mikef5410/USB_PressureSensor/app/OSandPlatform.h

#ifndef _OSandPlatform_INCLUDED
#define _OSandPlatform_INCLUDED

#ifdef GLOBAL_OSandPlatform
#define OSandPlatformGLOBAL
#define OSandPlatformPRESET(A) = (A)
#else
#define OSandPlatformPRESET(A)
#ifdef __cplusplus
#define OSandPlatformGLOBAL extern "C"
#else
#define OSandPlatformGLOBAL extern
#endif	/*__cplusplus*/
#endif				/*GLOBAL_OSandPlatform */

#ifdef __cplusplus
extern "C" {
#endif


/// \addtogroup lowlevel
/// @{
#include <FreeRTOS.h>
#include <task.h>
#include <queue.h>
#include <semphr.h>
#include <timers.h>

//#pragma GCC diagnostic push
//#pragma GCC diagnostic ignored "-Wpointer-sign"
//#pragma GCC diagnostic pop

#include <stdlib.h>
#include <stdarg.h>
#include <stdio.h>
#include <ctype.h>
#include <string.h>
#include <math.h>
#include <stdint.h>
#include <strings.h>
#include <limits.h>
#include <malloc.h>
#include <machine/endian.h> // /opt/gcc-arm-none-eabi-5_4-2016q3/arm-none-eabi/include/machine

#include <libopencmsis/core_cm3.h>
#include <libopencm3/stm32/gpio.h>
#include <libopencm3/stm32/rcc.h>
#include <libopencm3/cm3/scb.h>
#include <libopencm3/cm3/systick.h>
#include <libopencm3/cm3/nvic.h>
#include <libopencm3/usb/usbd.h>
#include <libopencm3/stm32/flash.h>
#include <libopencm3/stm32/desig.h>
#include <libopencm3/stm32/spi.h>
#include <libopencm3/stm32/i2c.h>
  
#include <libopencm3/stm32/f3/nvic.h>
  
#include "version.h"
#include "endian.h"
#include "bsp.h"  
#include "hiresTimer.h"
#include "usbcmdio.h"
#include "instr_task.h"  
  
#define TESTEEPROM 1
#include "eeprom9366.h"
#include "ms8607.h"
#include "SSCDANN150PG2A3.h"

//#define CEXCEPTION_USE_CONFIG_FILE
//#include "CException.h"

#ifdef __cplusplus
extern "C" {
#endif

//Chip driver status return values
typedef int32_t ChipDriverStatus_t;

#define SUCCESS 0
#define FAILURE 1
#define DO_NOT_TX -1
#define SATURATED 101
#define TRUE 1
#define FALSE 0
  
#ifndef RELEASE
#define ASSERT(EXPR) assert(EXPR)
#else
#define ASSERT(EXPR)
#endif

#define likely(x)       __builtin_expect((x),1)
#define unlikely(x)     __builtin_expect((x),0)

#ifndef MIN
#define MIN(a,b) (a<=b)?(a):(b)
#endif

#ifndef MAX  
#define MAX(a,b) (a>=b)?(a):(b)
#endif
  
//Trigger a HARD FAULT by writing to a FLASH ROM location
#define TRIG_HARDFAULT *((volatile int*)(0x8000000))=0
    
//We'll define this later
    typedef void BaseSequentialStream;

// HACK HACK HACK
// TEMPORARY HACK TO MAKE PRINTF WORK WITHIN FREERTOS TASKS
    OSandPlatformGLOBAL char pbuf[1024];
    extern int myprintf(const char *format, ...);
    extern int mysprintf(char *out, const char *format, ...);
    extern int mysnprintf(char *buf, unsigned int count,
			  const char *format, ...);

#define ENABLE_DEBUG_TASK 1

#ifdef RELEASE
#define DPRINTF(...)
#define FDPRINTF(FILE,...)
#define dprintf(...)
#else
#define DPRINTF(...) myprintf(__VA_ARGS__)
#define FDPRINTF(FILE,...) myprintf(__VA_ARGS__)
#define dprintf(...) myprintf(__VA_ARGS__)
#endif


#define delayms(x) do { if (xTaskGetSchedulerState() == taskSCHEDULER_RUNNING) { \
    vTaskDelay((x)/portTICK_RATE_MS);                                   \
  } else { \
    MSleep(x); \
  }  } while(0)


  
typedef struct task_info {
  uint32_t ExceptionTaskID;
} task_info_t;
    
OSandPlatformGLOBAL uint32_t numRegisteredTasks;	//main.c


extern char __StackTop;
extern char __StackLimit;
extern char __heap_start;
extern char __heap_end;

#ifdef __cplusplus
}
#endif

#endif				//OSandPlatform_INCLUDED

/// @}
