mikef5410/USB_PressureSensor/app/eeprom9366.c

/*******************************************************************************
*           Copyright (C) 2015 Michael R. Ferrara, All rights reserved.
*
*                       Santa Rosa, CA 95404
*                       Tel:(707)536-1330
*
* Filename:     eeprom9366.c
*
* Description: EEPROM9366 "driver"
*
*******************************************************************************/
//#define TRACE_PRINT 1

#include "OSandPlatform.h"

#define GLOBAL_EEPROM9366
#include "eeprom9366.h"

// This device has 9 bits of address, led by a three bit cmd.
// Data is 8 bit bytes.


static uint32_t writeEnabled = 0;

static inline void assertCS()
{
  //taskENTER_CRITICAL();
  gpio_set(GPIOB,GPIO9);
  //delayms(1); //Tcss
  return;
}

static inline void deassertCS()
{
  delayms(1); //Tcsl
  gpio_clear(GPIOB,GPIO9);
  //taskEXIT_CRITICAL();
  return;
}

static inline uint8_t spiTransaction(uint8_t command, uint16_t address, uint8_t data)
{
  uint8_t rbyte = 0;

  uint8_t b1 = (command<<2) | ((address & 0x180)>>7);
  uint8_t b2 = (address & 0x7f)<<1 | ((data & 0x80)>>7); 
  uint8_t b3 = (data & 0x7f)<<1;
  
  //printf("OUT: 0x%02x, 0x%04x, 0x%02x\n",command, address, data);
  //printf("Trans: 0x%02x 0x%02x 0x%02x\n",b1,b2,data);

  //Wait for Tx empty
  while (!(SPI_SR(SPI2) & SPI_SR_TXE));
  rbyte = SPI_DR(SPI2); // Clear the rx buffer
  rbyte = SPI_DR(SPI2); // Clear the rx buffer
  rbyte = SPI_DR(SPI2); // Clear the rx buffer
  rbyte = SPI_DR(SPI2); // Clear the rx buffer
  
  assertCS();
  // Byte 1 ... 3 bits of command + 9th bit of address
  spi_send8(SPI2,b1);
  (void)spi_read8(SPI2);

  // Byte 2 ... 8 bits of address,
  spi_send8(SPI2,b2);
  (void)spi_read8(SPI2);
 
  // Byte 3
  spi_send8(SPI2,b3);
  rbyte=spi_read8(SPI2);
  deassertCS();

  return(rbyte);
}

static inline void spiCMD(uint8_t command, uint16_t address)
{

  uint8_t b1 = (command<<1) | ((address & 0x100)>>8);
  uint8_t b2 = address & 0xff;
  uint8_t r;
  //printf("OUT: 0x%02x, 0x%02x\n",command, address);
  //printf("Trans: 0x%02x 0x%02x\n",b1,b2);

  //Wait for Tx empty
  while (!(SPI_SR(SPI2) & SPI_SR_TXE));
  r = SPI_DR(SPI2); // Clear the rx buffer
  r = SPI_DR(SPI2); // Clear the rx buffer
  r = SPI_DR(SPI2); // Clear the rx buffer
  r = SPI_DR(SPI2); // Clear the rx buffer
  (void)r;
  
  assertCS();
  
  // Byte 1 ... 3 bits of command + 1 bit of address
  spi_send8(SPI2,b1);
  (void)spi_read8(SPI2);
  
  // Byte 2 ... 8 bits of address
  spi_send8(SPI2,b2);
  (void)spi_read8(SPI2);
  
  deassertCS();
  return;
}

static inline void writeEnable()
{
  if (writeEnabled) return;
  spiCMD(0x4,0x180);
  writeEnabled=1;
  return;
}

EEPROM9366GLOBAL void eeprom9366_eraseAll()
{
  writeEnable();
  spiCMD(0x4, 0x100);
  delayms(10);
}

EEPROM9366GLOBAL void eeprom9366_erase(uint16_t address)
{
  writeEnable();
  spiCMD(0x7,address);
  delayms(10);
  return;
}


EEPROM9366GLOBAL void eeprom9366_write(uint16_t address, uint8_t data)
{
  writeEnable();
  (void)spiTransaction(0x5,address,data);
  delayms(10);
  return;
}


EEPROM9366GLOBAL uint8_t eeprom9366_read(uint16_t address)
{
  uint8_t res = spiTransaction(0x6,address,0);
  return(res);
}

EEPROM9366GLOBAL void eeprom9366_init()
{

  //SPI2 pins for EEPROM (Alternate function 5)
  //PB9 is SPI2NSS, PB8 is SPI2SCK
  //PB14 is SPI2MISO, PB15 SPI2MOSI
  //PCLK is 72MHz, so we need to select a baud rate divider
  //such that SPI CLK is less than 2MHz (32 -> 1.5MHz)
  rcc_periph_clock_enable(RCC_SPI2);
  gpio_mode_setup(GPIOB, GPIO_MODE_OUTPUT, GPIO_PUPD_NONE, GPIO9); //Software Slave-Select
  gpio_clear(GPIOB,GPIO9);
  gpio_set_output_options(GPIOB, GPIO_OTYPE_PP, GPIO_OSPEED_100MHZ, GPIO9);
  
  gpio_mode_setup(GPIOB, GPIO_MODE_AF, GPIO_PUPD_NONE,
                  GPIO8 | GPIO14 | GPIO15);
  gpio_set_af(GPIOB, GPIO_AF5, GPIO8 | GPIO14 | GPIO15);
  //gpio_set_output_options(GPIOB, GPIO_OTYPE_PP, GPIO_OSPEED_100MHZ,
  //                               GPIO8 | GPIO15); //SCK and MOSI are driven
  

  spi_set_master_mode(SPI2);
  spi_set_baudrate_prescaler(SPI2, SPI_CR1_BR_FPCLK_DIV_64); // 72/64 = 1.125MHz
  spi_set_clock_polarity_0(SPI2);
  spi_set_clock_phase_0(SPI2);
  spi_set_full_duplex_mode(SPI2);
  spi_set_unidirectional_mode(SPI2); /* bidirectional but in 3-wire */
  spi_set_data_size(SPI2, SPI_CR2_DS_8BIT);
  spi_enable_software_slave_management(SPI2);
  spi_send_msb_first(SPI2);
  spi_set_nss_high(SPI2);
  //spi_enable_ss_output(SPI2);
  spi_fifo_reception_threshold_8bit(SPI2);
  SPI_I2SCFGR(SPI2) &= ~SPI_I2SCFGR_I2SMOD;
  spi_enable(SPI2);
  spi_disable_crc(SPI2);
  spi_set_next_tx_from_buffer(SPI2);
 
  return;
}

#ifdef TESTEEPROM
EEPROM9366GLOBAL void eeprom9366_test()
{

  uint8_t d;
  
  printf("SPI_CR1: 0x%04x\n",(uint16_t)SPI_CR1(SPI2));
  printf("SPI_CR2: 0x%04x\n",(uint16_t)SPI_CR2(SPI2));
  printf("SPI_SR: 0x%04x\n",(uint16_t)SPI_SR(SPI2));
 
  myprintf("EEProm Test\n");
  eeprom9366_eraseAll();
  myprintf("Erase complete\n");
  d = eeprom9366_read(0x10);
  myprintf("EEPROM read after erase: 0x%x\n",d);
  eeprom9366_write(0x10,0x41);
  d = eeprom9366_read(0x10);
  myprintf("EEPROM read after write (0x41): 0x%x\n",d);
  d = eeprom9366_read(0x11);
  myprintf("EEPROM read after write of next cell : 0x%x\n",d);

  eeprom9366_write(0x11,0x01);
  eeprom9366_write(0x12,0x2);
  eeprom9366_write(0x13,0x3);

  printf("Write/read block ... should be 0x41,1,2,3,0xff:\n");
  uint8_t a;
  for (a=0x10; a<=0x14; a++) {
    d= eeprom9366_read(a);
    printf(" 0x%02x",d);
  }
  printf("\n");

  eeprom9366_erase(0x10);
  d = eeprom9366_read(0x10);
  myprintf("EEPROM read after cell erase: 0x%x\n",d);

  return;
}
#endif
